NilujePerchut/kbd75mockv2/doc/iso.png

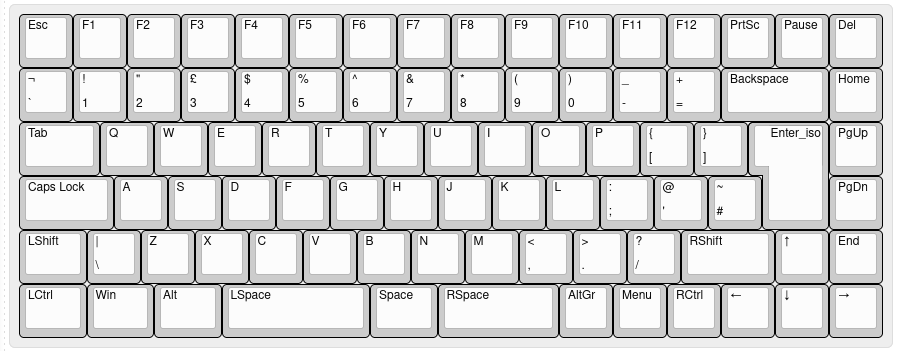
doc/iso.png
