NilujePerchut/kbd75mockv2/doc/Layouts.png

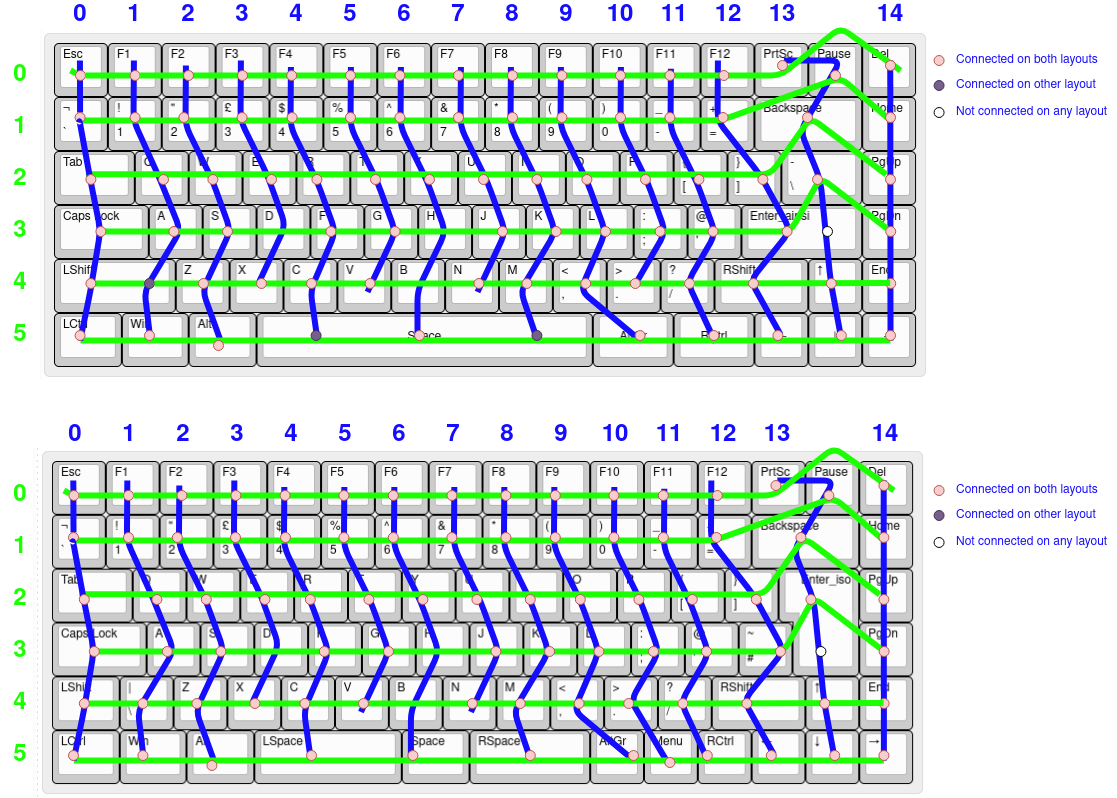
doc/Layouts.png
