NilujePerchut/kbd75mockv2/doc/references/key profiles.jpg

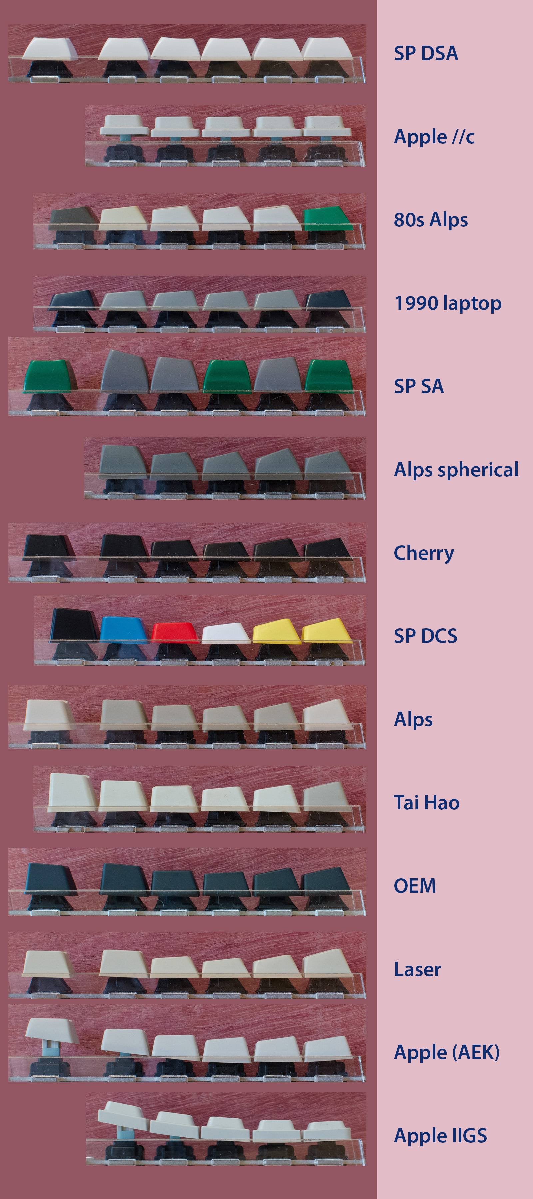
doc/references/key profiles.jpg
