NilujePerchut/kbd75mockv2/doc/references/YMDK.jpg

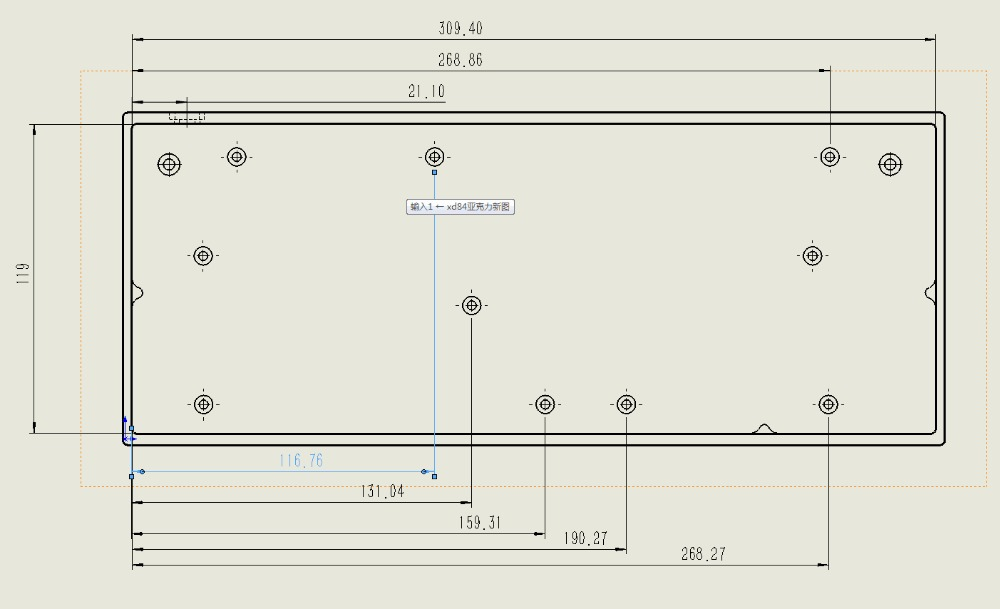
doc/references/YMDK.jpg
